Amodo-Design/PSRR-Injector-Board/simulation/psrr.asc

C1: cap; 220µ; V=100 Irms=0.66 Rser=0.23 Rpar=1000Meg
C2: cap; 220µ; V=100 Irms=0.66 Rser=0.23 Rpar=1000Meg
C3: cap; 220µ; V=100 Irms=0.66 Rser=0.23 Rpar=1000Meg
C4: cap; 220µ; V=100 Irms=0.66 Rser=0.23 Rpar=1000Meg
C5: cap; 220µ; V=100 Irms=0.66 Rser=0.23 Rpar=1000Meg
C6: cap; 220µ; V=100 Irms=0.66 Rser=0.23 Rpar=1000Meg
C7: cap; 220µ; V=100 Irms=0.66 Rser=0.23 Rpar=1000Meg
C8: cap; 220µ; V=100 Irms=0.66 Rser=0.23 Rpar=1000Meg
L1: WE-SL2
L2: WE-SL2
L3: WE-SL2
L4: WE-SL2
R1: res; 5
R3: res; 100
R4: res; 100
R5: res; 50R
V1: voltage; 30V
V2: voltage; 30V
V3: voltage; SINE(0 1 100k); AC 1
Named nets: 0, Vinj, Vout+, Vout-, Vdamp
.tran 10m
.ac dec 1000 0.1 100Meg
.include WE-SL2.lib
